misch2/ups12v/hardware/v2/bq25798_module/pdfs/bq25798_module-In1_Cu.pdf

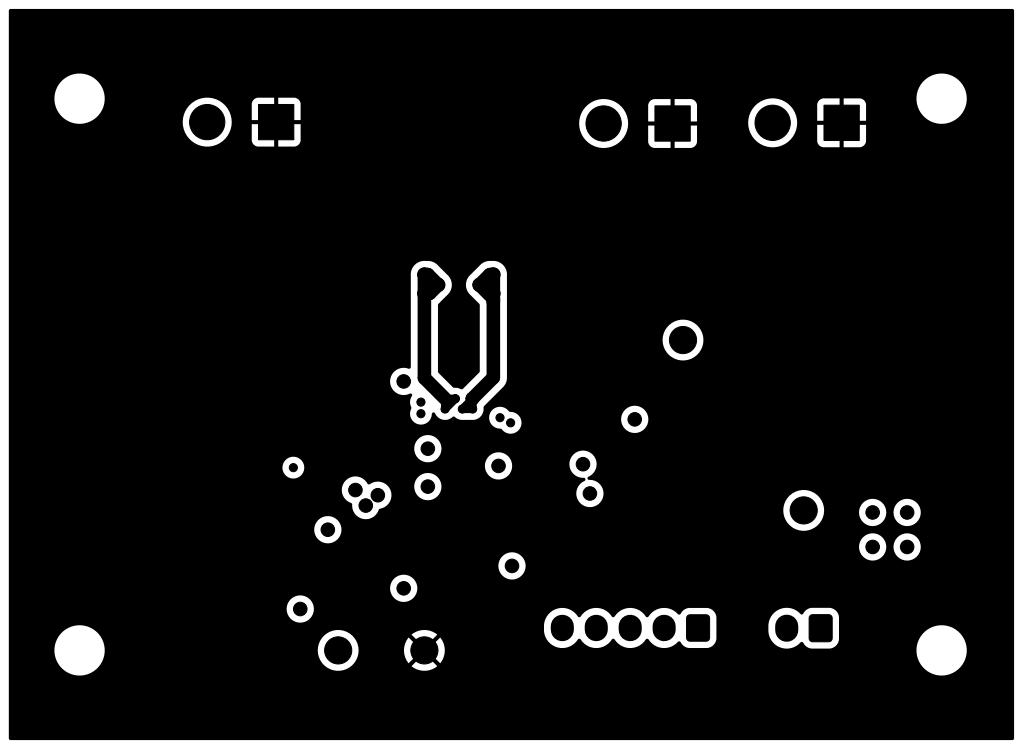
[picture p15: page 1]
