misch2/ups12v/hardware/v2/bq25798_module/pdfs/bq25798_module-In2_Cu.pdf

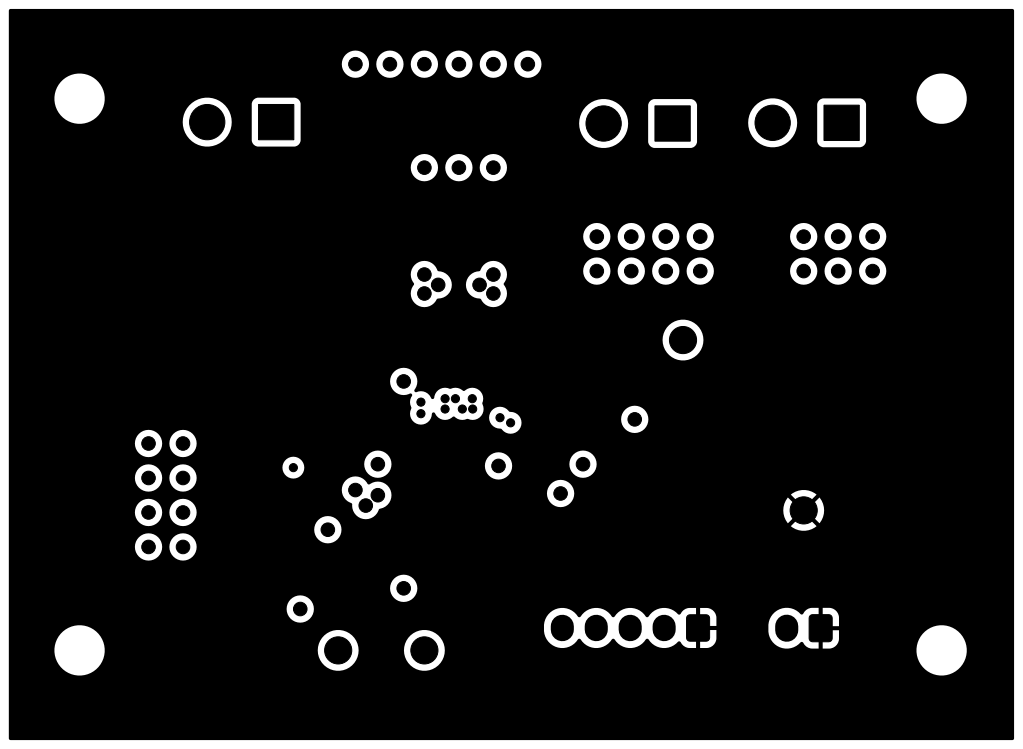
[picture p16: page 1]
