misch2/ups12v/hardware/v2/bq25798_module/pdfs/schematics.pdf

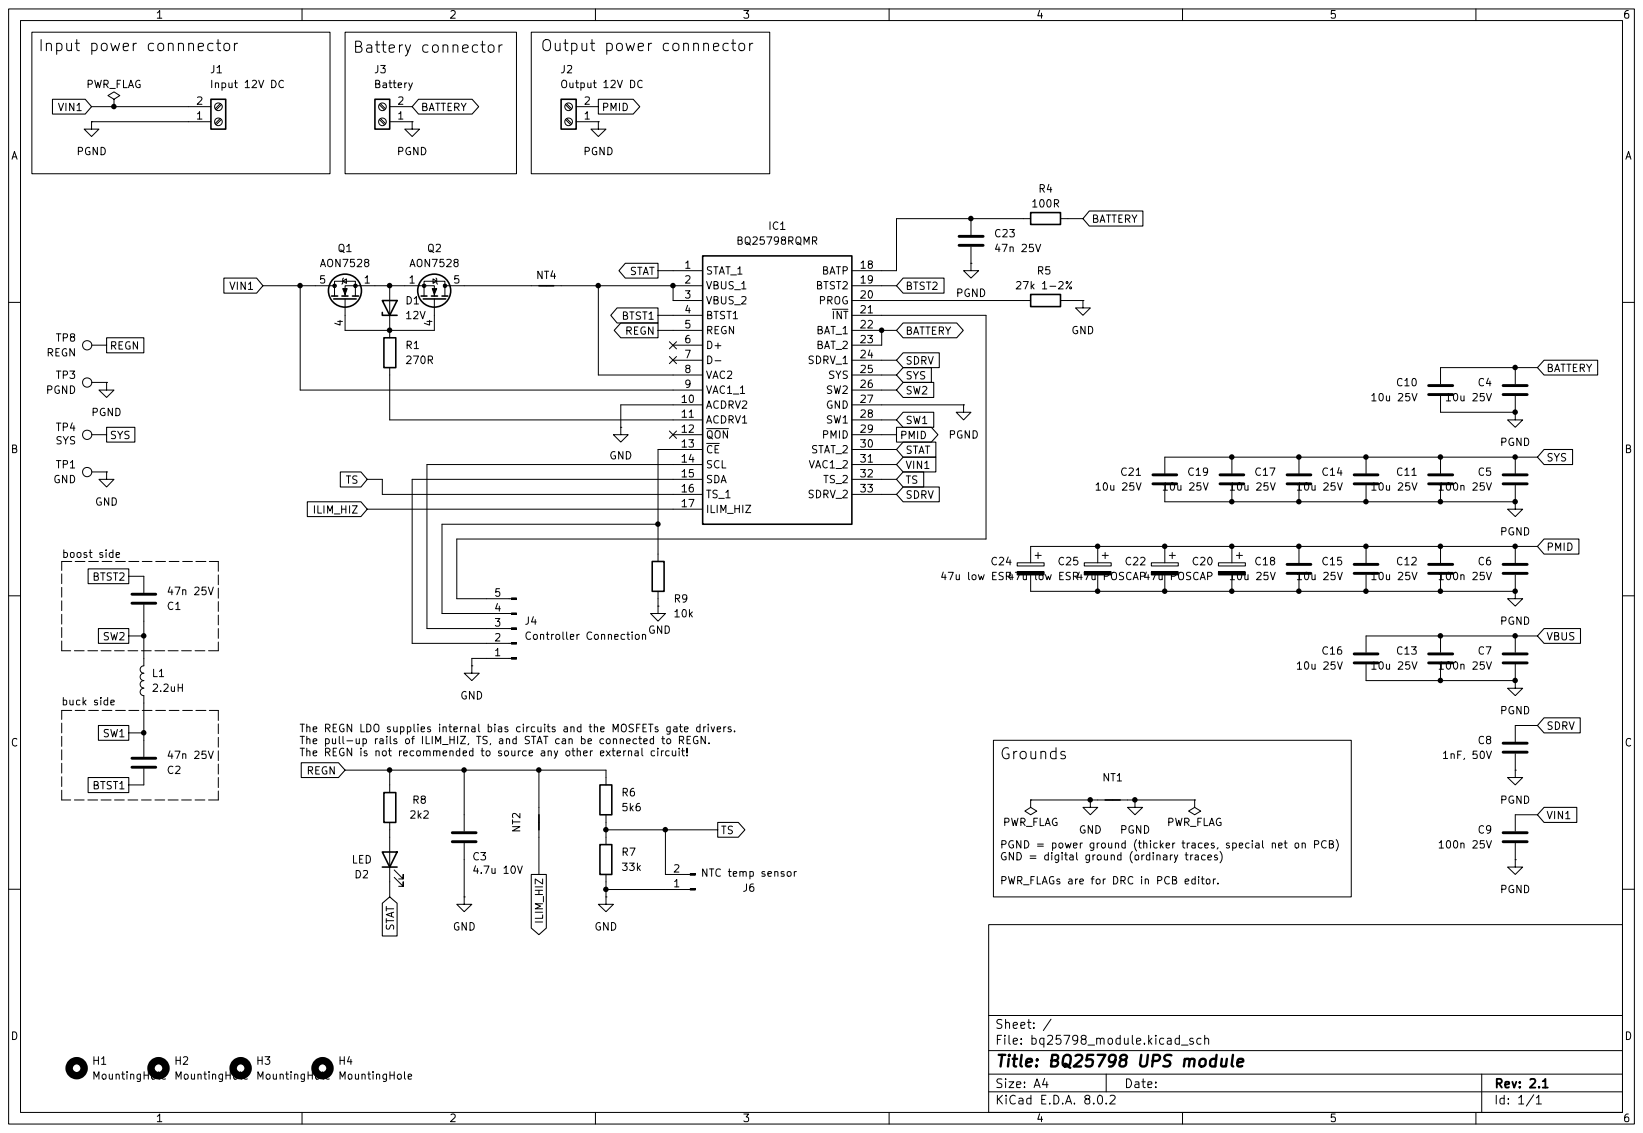
[picture p17: page 1]
