misch2/ups12v/hardware/v1/pcb.pdf

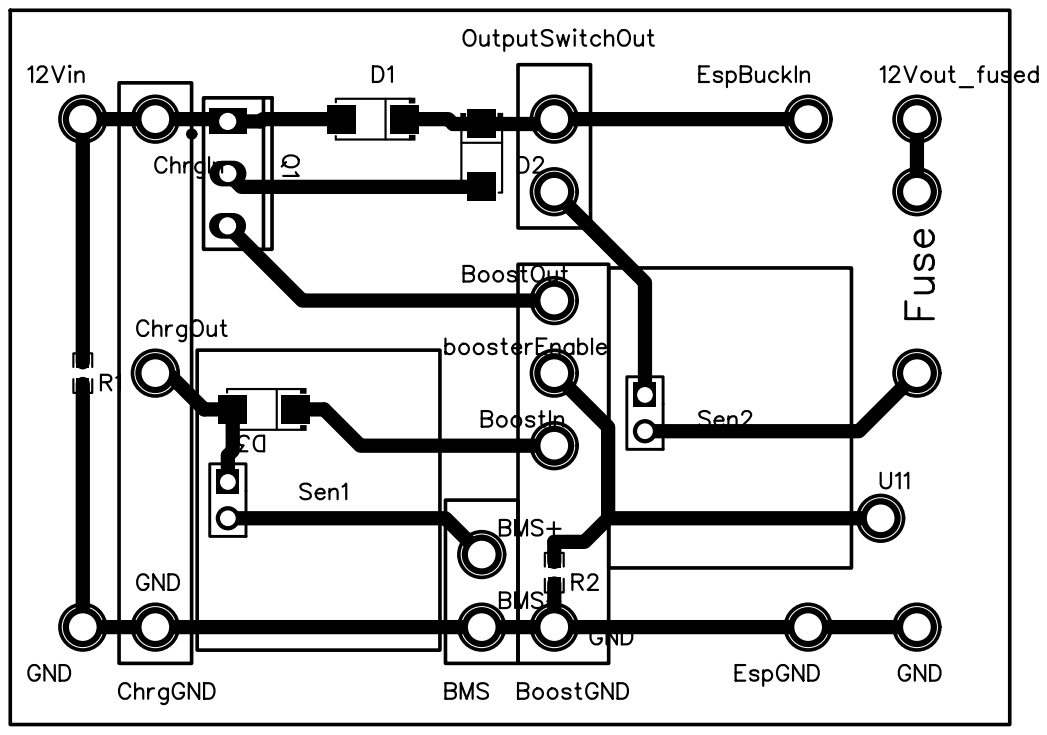
[picture p18: page 1]
