misch2/ups12v/hardware/v1/schema.pdf

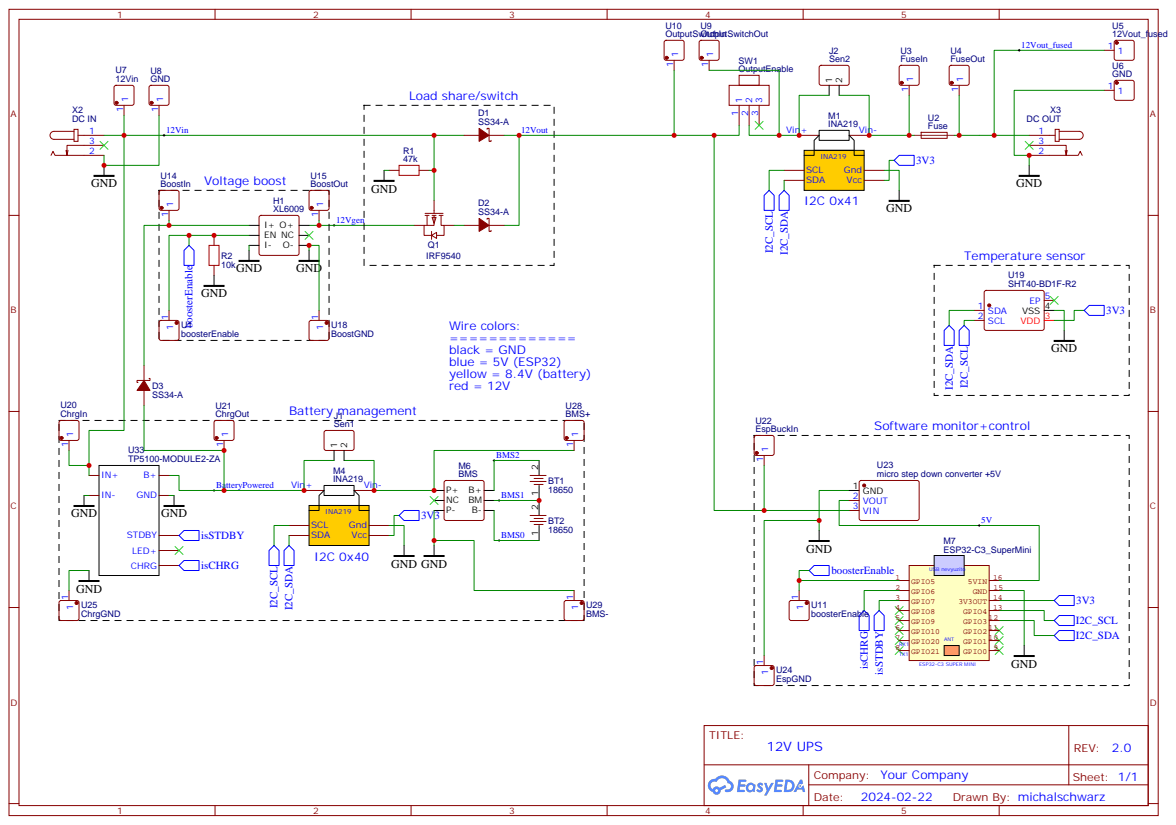
[picture p19: page 1]
